ideocentric/caryatid/docs/indicators.md

# Indicators

Three indicators, and the reason there are three rather than one is a power
domain problem, not a design preference.

## The constraint

**Charging happens while the instrument is switched off.** The RGB LED hangs on
Seed GPIOs, and those are dark when the Seed is unpowered. So of the four states
worth showing, two cannot come from firmware at all:

| State | Needs the Seed powered? |
| --- | --- |
| Battery low while playing | yes — fine |
| Fault / warning | yes — fine |
| **Charging** | **no** |
| **Charge complete** | **no** |

Anything that must be readable with the instrument off has to be driven by
hardware. That is the whole argument.

## The three

**1. Switch lamp — power state.** The illuminated latching switch, fed from the
**5.0 V** boost rail. The switch asserts the boost's EN; the boost comes up; the
lamp lights. Off means genuinely off, with no firmware in the loop.

The lamp's **current limiting is internal**, so `R_LED` is a 0 Ω link. Keep the
0603 footprint so a different switch can be dropped in without a board change,
and because fitting a real resistor there is how this lamp gets dimmed if it is
ever wanted dimmer.

**Measured 2026-09-20**, and the part in hand is marked **3–6 V**, not the 3–9 V
variant this section was originally written against:

| Across the lamp | Current |
| --- | --- |
| 3.00 V | 5.6 mA |
| **5.00 V, the rail in service** | **28.5 mA** |
| 6.00 V, top of the marking | 39.9 mA *(extrapolated)* |

🔴 **The internal limiting is a plain series resistor, not a current source**:
three points fit Vf ~2.51 V with ~87.5 Ω to within 1%. A voltage-*range* marking
means the part tolerates the range, **not** that the current is constant over
it. Here it tracks the rail almost 8:1 end to end, which is why the budget
figure is quoted against a rail voltage.

**The brightness question is settled, and this section's own prediction was
right.** It said, conditionally, that a plain series resistor would give
"roughly 75% of the current" at 5 V against the 4×AA (~6 V) reference the
brightness was judged by. It is a plain series resistor and the real ratio is
28.5 / 39.9 = **71%**, which the eye reads as around 89% as bright. Almost
certainly indistinguishable, and comfortably inside a range the lamp already
sees on depleted NiMH. **No action, and no board change.**

**That reading is also the switch lamp's line in the 5 V budget**, where it was
the largest of three entries marked unknown and is now closed. It is the
**largest indicator load on the rail**, ahead of the RGB with all three dies
lit, and unlike the RGB it is lit whenever the instrument is on. See the
line-item table in [values.md](values.md) and
[`panel-latch-switch`](../discovery/findings/panel-latch-switch.yaml).

**2. Charge LED — charge state, hardware only.** Driven directly from the
bq24074's open-drain `/CHG` and `/PGOOD` off the OUT rail, via J4. **This is the
indicator that satisfies the charge-complete-while-off requirement**, and it is
the only one that must exist. Nothing about it depends on firmware running.

### One bicolour LED instead of two singles

J4 already carries a red/green **common-anode bicolour** with no board change. A
part like that has exactly three terminals and they land on pins 1–3 as they
stand; pin 4 stays unused, as it is now.

| J4 pin | Net | Bicolour |
| --- | --- | --- |
| 1 | `VOUT` | common anode |
| 2 | R9 1 kΩ → `~{CHG}` | red cathode |
| 3 | R10 1 kΩ → `~{PGOOD}` | green cathode |
| 4 | `GND` | unused |

It reads better than two separate LEDs, because the charger's two open-drain
outputs mix in one lens:

| `/CHG` | `/PGOOD` | Colour | Meaning |
| --- | --- | --- | --- |
| high-Z | high-Z | **off** | on battery, no charger |
| low | low | **amber** | charging |
| high-Z | low | **green** | external power, charge complete |
| low | high-Z | red | anomalous; should not occur |

Amber-while-charging going green-when-done is read without a legend, and it
matches the *off means fine* logic the RGB already uses.

> **The green die decides whether this works, and J4 runs from `VOUT`.** That is
> the cell, not a regulated rail — roughly **4.2 V falling to ~3.0 V** in use. An
> **AlGaInP** yellowish-green around 2.1 V is fine across the whole range. An
> **InGaN true green at 3.0–3.2 V will dim and then go dark as the cell drains**,
> and no resistor value fixes it. This is the same physics that stops the RGB
> being driven from 3V3, one rail down.

Current, with the dies now **measured** rather than assumed at ~2.1 V:

| Cell | Red | Green | Amber total |
| --- | --- | --- | --- |
| 4.2 V, full | 2.33 mA | 1.88 mA | 4.2 mA |
| 3.0 V, flat | 1.19 mA | 0.77 mA | 2.0 mA |

Each status pin sinks only its own, well inside the 15 mA limit. *(This section
read "2.1 mA per die" until 2026-09-22, derived from an assumed 2.1 V green. The
real green is 2.322 V, making it 1.88 mA. The 4.2 mA amber total survived the
correction by accident, since red's surplus covers green's shortfall.)*

**Expect to trim the balance**, and the direction is now measured: **red draws
24% more current than green** through equal resistors, on top of being the
brighter die per milliamp. R9 and R10 are separate resistors for exactly that.

🔴 **But the balance is not a fixed adjustment, it moves with state of charge.**
Green's higher forward voltage eats proportionally more of a shrinking headroom,
so green fades 2.4× across the cell's life while red fades 2.0×, and the amber
drifts toward red: a current ratio of 1.25 on a full cell against **1.55 on a
flat one**. Trim at mid-cell rather than on a freshly charged pack. Resistors can
centre this; they cannot stop it moving, because it is driven by the Vf
difference against a falling rail. Harmless, and arguably it reads correctly, but
it should not be rediscovered later and mistaken for a fault. See [`j4-charge-led`](../discovery/findings/j4-charge-led.yaml).

Part choice and its open question are in [sourcing.md](sourcing.md).

**3. RGB — everything else, firmware driven.** J12, on D26/D27/D29. Solid on/off
mixing only; no PWM.

> **It cannot be driven from a 3V3 GPIO.** Green and blue have forward voltages
> around 3.0-3.1 V against an output-high of roughly 3.15 V — they will not
> light, and no resistor value fixes it. **Common anode to the 5 V rail with the
> GPIOs sinking.** See [values.md](values.md).

**Tolerance confirmed against the datasheet**, not assumed. `DS12556` Rev 8,
Table 7, via the Daisy-to-STM32 mapping in `Seed_pinout.csv`:

| Daisy | STM32 | I/O structure | |
| --- | --- | --- | --- |
| D26 red | PD11 | **FT_h** | 5 V tolerant, high-speed low-voltage |
| D27 green | PG9 | **FT_h** | 5 V tolerant, high-speed low-voltage |
| D29 blue | PB14 | **FT_u** | 5 V tolerant, USB option on VDD33USB |

`FT` is 5 V tolerant, `TT` would be 3.3 V only. Positive injection is not
possible on an FT pin — there is no upper clamp to VDD, which is what the
tolerance consists of. Sink is 20 mA per I/O against the ~5 mA per channel here.

> **FIRMWARE: the internal pull-up and pull-down must stay disabled on D26, D27
> and D29.** `DS12556` Table 9 note 4: *"To sustain a voltage higher than 4 V the
> internal pull-up/pull-down resistors must be disabled."* These pins sit at the
> full 5 V whenever their LED is off, because the anode is on the 5 V rail. A
> GPIO configured with either pull enabled is outside the absolute maximum
> rating. Push-pull or open-drain output with no pull, and nothing else.

Files and links for both documents are in [datasheets.md](datasheets.md).

## RGB states

Seven colours from on/off mixing, urgency carried by blink rate, and **off means
fine** — which is what you want on a stage.

| Condition | Colour | Pattern | Source |
| --- | --- | --- | --- |
| Playing, battery OK | off | — | — |
| Battery low — head for a socket | amber | slow, 1 Hz | A10 |
| Battery critical | red | fast, 4 Hz | A10 |
| Fault | magenta | fast, 4 Hz | A10 + A11 |
| Charging | blue | solid | A11 |
| Charge complete | green | solid | A11 |

Cyan and white are deliberately unassigned. A spare state is worth more than an
exhaustive palette.

Firmware can show charge state on the RGB *while the instrument is on* because
it reads charge status from A11 — that is a convenience, not the mechanism that
satisfies the off-state requirement.

## Faults worth signalling

Magenta means something specific, or it means nothing:

- charger thermal fault or charge-timer expiry, via the `/CHG` behaviour on A11
- cell voltage critically low, via A10
- **cell disconnected or its protection tripped** — A10 reads near zero while
  the OUT rail is alive. Worth catching before a gig rather than during one.

## Charge status on one analogue pin

`/CHG` and `/PGOOD` are both open-drain, and the pin budget had no room for two
digital inputs. A11 had no other job, so both signals are encoded onto it as
four voltage levels: a pull-up to 3V3 and two different-valued pull-downs.

```
        3V3 ──[ 10k ]───┬──[ 1k ]──┬── A11
                        │          │
        /CHG ──[ 10k ]──┤        [10nF]
                        │          │
      /PGOOD ──[ 20k ]──┘         GND
              (2 x 10k series)
```

**Four resistors of one value** — the 0.1% 10 k already in stock (C374544).

| `/CHG` | `/PGOOD` | State | Level | Counts |
| --- | --- | --- | --- | --- |
| high-Z | high-Z | idle, on battery | 3.300 V | 4095 |
| high-Z | low | external power, not charging | 2.200 V | 2730 |
| low | high-Z | charging | 1.650 V | 2048 |
| low | low | charging, external present | 1.320 V | 1638 |

Minimum separation **330 mV** — 409 ADC counts — and because the parts are 0.1%
the worst case is **329 mV**, which is to say the nominal.

**Decode by nearest level, not by thresholds.** The bands cannot be confused, and
nearest-neighbour needs no constants that can later drift out of date.

### How the values were arrived at

A search over E24 maximising the minimum separation gives **10 k / 11 k / 18 k**
and 390 mV, against roughly 150 mV for the naive first pick. Monte-Carlo over
tolerance showed that network holding up well:

| Tolerance | Worst gap | Bands overlap |
| --- | --- | --- |
| 1% | 377 mV | no |
| 5% | 312 mV | **no** |

That it still works at 5% is what made the substitution safe. Separation here is
a threshold to clear, not a score to maximise: at 330 mV the closest two states
are 409 ADC counts apart, against noise of a few counts, so both networks are
unambiguous by a wide margin and the extra 60 mV is headroom nothing will ever
use. Meanwhile three values cost three BOM lines and three feeder positions
where one costs one — and the stocked part is 0.1%, so the one-value network's
worst case is 329 mV against its 330 mV nominal. Less accurate on paper, more
accurate in the drawer, cheaper to build. Reasoning in full in
[sourcing.md](sourcing.md).

Two things that are not obvious either way:

- **The levels depend only on the ratios**, so the network scales freely. 10 k is
  the largest value that keeps the ADC source impedance sane; scaling down only
  burns current for nothing.
- **The pull-up sits on 3V3, the Seed's rail**, so the network draws nothing
  while the instrument is off. The charger's status pins are alive then, but with
  no pull-up there is no path. Unlike the A10 battery divider, this costs no
  standby current at all.

`1k + 10nF` mirrors the A10 filter, and the capacitor is doing real work: at 10k
source impedance the ADC's sample-and-hold cannot charge fast enough on its own,
so the cap supplies it and the 10k merely tops the cap back up between samples.
**Use a long ADC sample time on A11 regardless.**

This also delivers requirement P-8 — charge state exposed to the MCU, not only
to LEDs — which had no implementation before.

## What is deliberately not here

**No PWM on the RGB.** Solid mixing only. Seven states is enough, and dimming a
status LED on a stage instrument is a feature nobody has asked for.

**No firmware involvement in the power lamp.** It follows the rail. A power
indicator that depends on software is a power indicator that lies during a hang.
