ideocentric/caryatid/docs/conventions.md

# Conventions for the tools

Rules that apply to **more than one tool**, and that each cost something to
learn. Every one of these lived in a single tool's docstring, where the next
tool to make the same mistake could not see it.

These are not style preferences. Each entry states the rule, the failure that
produced it, and the measurement that proves it — so a future change can tell
whether it is still true rather than taking it on faith.

For decisions about the *board*, see [decisions/](decisions/). This file is
about the code that edits it.

---

## 1. Recompute the zone fill before verifying a copper change

**Any tool that widens, moves, or adds copper must refill the zones before it
asks DRC whether the result is legal.**

A pour holds its clearance from a track by *retreating from it*. Change the
copper and check without refilling, and DRC compares new copper against a pour
drawn for the old geometry. The gap it measures is a fill artefact — a number
describing a board that will never be fabricated.

**What it cost.** `widen_necks.py` widened five Freerouting neck-downs to the
0.20 mm floor and DRC reported one new clearance violation:

```
zone clearance 0.3000 mm; actual 0.2630 mm
Track [/power/TMR] on F.Cu  vs  Zone 'GND plane' [GND]
```

0.263 is 0.300 minus half the 0.075 mm the track grew — the pour standing still.
Tested one at a time, **four of the five were already clean** and only TMR
"failed", against a fill that had not moved. The tool's all-or-nothing rule then
reverted all five. It had been printing "those necks are LOAD-BEARING … it needs
routing space, which is a placement question" since `a68ae67`. They were not,
and it did not.

**The tell:** the conflict was with a **zone**, which retreats, rather than with
a pad or another track, which cannot. A clearance violation against a pour, on
copper you just changed, is suspect until you have refilled.

```python
KPY = ".../Python.framework/Versions/3.9/bin/python3"
subprocess.run([KPY, "-c",
    f"import sys;sys.path.insert(0,'{KSP}');import wx;wx.App(False);"
    f"import pcbnew;b=pcbnew.LoadBoard('{path}');"
    f"pcbnew.ZONE_FILLER(b).Fill(b.Zones());pcbnew.SaveBoard('{path}',b)"])
```

`import wx; wx.App(False)` first — pcbnew's Python needs a wxApp to exist before
`ZONE_FILLER` runs, the same requirement `ImportSpecctraSES` has. It still
prints `create wxApp before calling this` on stderr and completes correctly;
that line is noise, not a failure.

**All-or-nothing verification is still right** — a half-widened board reads as
deliberate — but it multiplies the damage of a bad check. One false positive
reverted four sound repairs. Verify the board that would be fabricated.

---

## 2. Collect edits first, apply back to front, and check structure not just parens

Editing s-expression text while iterating over matches shifts every later
offset. Collect all `(offset, old, new)` first, then apply in **one** pass
sorted descending.

**"One pass" is load-bearing, and two descending passes are not equivalent.**
`silk_centre_roles.py` applied footprint-property edits and text edits in two
separate back-to-front passes, both measured against the same original string.
The first pass shifted the file under the second, and `ANALOG BUS` was spliced
inside another label's `(effects)` block.

**Parenthesis balance did not catch it**, because a splice moves parens without
changing their count. `lock_copper.py` corrupted the board the same way earlier,
dropping two segments while staying balanced. Balance is necessary and nowhere
near sufficient. Check structure as well:

```python
if t[off:off + len(old)] != old:
    sys.exit("offset no longer holds what was measured -- not writing")
top  = len(re.findall(r"^\t\(gr_text ", t, re.M))
if top != t.count("(gr_text "):
    sys.exit("a gr_text is no longer at top level -- not writing")
```

What actually surfaced the corruption was `kicad-cli` refusing to parse the
file. **A tool that writes a board should run `kicad-cli pcb drc` afterwards and
treat a non-zero exit as a failed write**, not only as a DRC result.

---

## 3. The collision box must share the anchor the emitter uses

A geometry model that tests one box and draws another is worse than no model:
it reports clearances confidently and wrongly.

- **`conn_labels.py`** tested a **centred** box and emitted `(justify bottom)`,
  which anchors the *bottom*. Every label drew about half a line higher than
  what was checked. The model called J3 a comfortable 0.73 mm clear of
  `CHG LEDS` while DRC reported them overlapping, **six times**, across 22 silk
  violations.
- **`silk_align_connectors.py`** built every reference box horizontally while
  preserving each field's *stored* angle. J9's reference was stored at 90° and
  drew vertical, so a 1.96 × 1.15 box was checked where the board drew
  1.15 × 1.96. The model read 0.47 mm of clearance; DRC found **0.2433**.
- **`pin_labels.surviving_labels`** used `x + up` on both sides of rotated text.
  `th_split` divides line height *asymmetrically* about the anchor, so every
  rotated label got a box of the wrong height, off centre.
- **`check_schematic.py`** made the same mistake in a different file format, and
  it is worth seeing twice. A net label in a `.kicad_sch` is anchored at the end
  that touches the wire and grows away from it; a symbol field is centred. A
  first version treated labels as centred, which halved their reach and reported
  a sheet clean while a 300 dpi plot showed labels plainly over the resistors.
  On `audio.kicad_sch`, `BIAS_E_L` anchors 8.89 mm from R51 and its text runs
  back toward it.

  🔴 **REFUTED 2026-08-24, and the correction belongs here rather than in a
  quiet edit.** Fixing the anchor was necessary and not sufficient: the box was
  still too SHORT, because `CHAR_W` was 0.72 mm per character and had never been
  measured despite a comment saying it was. Measured at 600 dpi off the plot
  this tool checks, it is 1.08–1.19 (`'+5V_RAW'` 8.297 mm / 7, `'VOUT'`
  4.612 mm / 4, `'LEG_101_L'` 9.700 mm / 9). A 1.6× underestimate on every box.

  Everything that rested on it was wrong. `BIAS_E_L` does not clear R51 by
  0.59 mm, it runs **3.01 mm into it**. Thirty labels cross, not zero. And the
  five "cosmetic" crossings fixed by moving them 2.54 mm were sized from the
  same broken model, which called a 3 mm overshoot 0.13 mm — **the fix was
  scaled by the error it was correcting, so it could not have worked.**

  The rendered plot had shown this correctly at 100 dpi and again at 300, and was
  overruled both times by the model, because a number feels like evidence and a
  picture feels like an impression. Neither is evidence about the other: the
  plot IS the artefact being checked, and the model is only a claim about it.

  The general form of this (why the constant survived so long, and what a
  constant has to carry so it cannot) is **rule 10**. This entry is the local
  damage; rule 10 is the rule.

- **`check_schematic.py`'s border test, again, and this one was found by eye.**
  It compared the symbol **origin** against the frame and skipped every symbol
  whose reference starts with `#`. Both are the same error as above in a
  different disguise: a box smaller than the ink. C21 on `panel-io.kicad_sch`
  had its origin at y 407.67, inside the 410 frame, while its lower pin reached
  **411.48** — `Device:C` has a body half-height of 0.762 mm and pins reaching
  3.81 mm, a factor of five. Underneath it the `GND` flag sat at 416.56 with its
  bottom edge **0.9 mm from the paper edge**, and was never tested at all,
  because the `#PWR` filter written for the *label-crossing* check had been
  copied into the *border* check where it does not belong. A power flag is ink
  on the plot like anything else.

  The fix keeps `lib_extents()` body-only and adds a separate `lib_reach()`
  including pins, because the two checks ask different questions. "Does this
  label sit on the part" tolerates a label along a pin stub; "is any ink off
  the page" does not.

Where the anchor cannot be established, **over-reserve**. An obstacle model may
claim more space than the ink needs; it may never claim less.

**A filter is part of a check, not part of the file.** Three of the five misses
above are a box or an exclusion carried from the place it was correct into a
place it was not. When copying a guard between checks, restate what it is for;
if that sentence does not survive the move, neither should the guard.

---

## 4. `P.tw` is a bounding box, so centre with it and never right-align with it

`pin_labels.tw()` returns KiCad's bounding-box width — about 1.1× the inked
width plus a constant. That error is not uniform: it **grows with string
length**.

- **Centring is safe.** The surplus splits evenly either side of a centred
  anchor and cancels; the drawn centre is the anchor whatever the error.
- **Computing an edge is not.** Placing labels at `right - w/2` to right-align
  them indented `GND` about 0.11 mm further than `R`, because the 3-character
  string carries more surplus. The right edges were identical in the model and
  visibly ragged on the board.

To align an edge, emit `(justify right)` and let KiCad find the true edge. The
box then extends *leftward* from the anchor, where over-estimating is the safe
direction.

---

## 5. Silk geometry is centrelines; footprint bounding boxes include markers

Two distinct traps in reading a footprint's silkscreen.

**`fp_line` coordinates are the middle of a 0.12 mm stroke.** The drawn edge is
0.06 mm further out. `silk_audio_baseline.py` measured 0.280 mm of clearance
where DRC found **0.2158**, on J14 and J18. J17's outline ends 0.14 mm sooner
and passed — the kind of near-miss that makes a wrong model look right.

**The bounding box of *all* silk is not the body.** J5 and J11 are IDC box
headers carrying a pin-1 triangle *outside* the outline — J5's at
x 161.780‥162.780 against a body ending at 161.390. Centring on the union put
the label 0.695 mm off, while the body outline, the pad span and the courtyard
all independently agreed on 156.830. Group the segments into connected
components and take the largest; a detached marker then drops out by
construction, with no per-part exception list.

---

## 6. Normalise a lone outlier; exclude only what cannot be fixed

An allow-list is for defects that **cannot** be repaired. Reaching for one to
silence something cheap to fix hides a real inconsistency behind a written
excuse.

**R45** was flagged `lib_footprint_mismatch` because its pads were stored at
270° against a footprint at 90° — 180° *relative*, where `Resistor_SMD` has 0°.
It was **the only one of 64 0603 resistors** on this board like that. The half
turn was harmless (a 0.800 × 0.950 mm rectangle is unchanged by it, and both pad
centres are byte-identical before and after), which is exactly why excusing it
was wrong. It was normalised; the allow-list entry became a comment saying so.

**A1 and A2** are the opposite and belong in the list. All 20 pads of each were
diffed against `caryatid.pretty/DaisySeed_Socket_A_1x20.kicad_mod`: **none
differ**. What differs is what KiCad adds when a footprint is *placed* — `path`,
`sheetfile`, `sheetname`, two property fields and their hide flags. None of it
is copper, and none of it is removable without breaking the schematic link.

The test is not "is it harmless" — both were harmless. It is **"can it be
fixed"**.

---

## 7. Record a hand placement as an override rather than overwriting it

A generator that re-derives positions will revert a deliberate hand adjustment
on its next run, silently, and the person who made it will not be watching.

`silk_audio_baseline.py` carries `ROLE_OVERRIDE` and `REF_OVERRIDE` for J14,
whose `MIC RTN` and reference were placed by hand after the computed positions
read wrong on the shortest jack. Re-running the tool now reproduces the board
instead of fighting it.

Locks are not sufficient: a tool that strips and regenerates its own output by
uuid ignores them. Locks stop an accident; recording the intent stops a re-run.

---

## 8. A fact carried only in conversation will outlive its truth

Not a coding rule, but it cost the most sessions.

An "R45 sits 1.22 mm from the board edge, review with the enclosure in hand"
concern was repeated across four sessions and was never true after `3fe330e`
moved the part. Measured: **5.500 mm**, with J15 and J9 both reaching *further*
toward that edge than R45 does. It survived because it was never written into a
ledger record where it would have been re-checked — the precise failure
`~/.claude/CLAUDE.md`'s ledger methodology exists to prevent. It is now retired
as dated evidence on `BUD-CU-477-interior`.

If a claim matters enough to repeat, it belongs in
[discovery/findings/](../discovery/findings/), not in a summary.

---

## 9. A `.kicad_sch` is not a `.kicad_pcb`, in two ways that will bite

Both of these cost real time in `check_schematic.py`, and neither is guessable
from experience with the board format.

**A schematic embeds its symbol LIBRARY beside its placed instances, and the two
are indistinguishable by their opening line.** Both are `(symbol ...)` at the
same nesting. Matching both reported **49 symbols outside the page borders**,
with references like `J`, `C` and `R` carrying no number and coordinates near
the origin, because those were library definitions in symbol-local coordinates.

```python
if "(lib_id " not in blk:      # a placed instance has one; a definition does not
    continue
```

The real answer was **one** symbol, JP6 in a title block. A checker that
overcounts by fifty is worse than no checker: the finding that mattered was
buried in noise that looked identical to it.

**Property coordinates are ABSOLUTE in a schematic and RELATIVE in a board.** In
a `.kicad_pcb`, a footprint's Reference sits at an offset from the footprint
origin and has to be transformed by the footprint's rotation. In a
`.kicad_sch`, the same field carries a page coordinate directly. Verified rather
than assumed: R11's symbol sits at (190.5, 69.85) and its reference text at
(196.5, 39.85).

Carrying the board habit across produces offsets that look plausible and are
nonsense, which is the failure mode that does not announce itself.

**The corollary for symbol extents.** A placed instance does not record how big
its body is; that lives in the embedded library definition, in symbol-local
coordinates. Any check that needs a body size has to read `lib_symbols` and
match on `lib_id`, or guess. A guess that fits a resistor is wrong for a
twenty-pin connector, and a check calibrated on passives will silently miss
every collision on the parts that matter.

---

## 10. An empirical constant carries its measurement, or it is a guess wearing a lab coat

**Any constant standing in for a physical measurement must record the raw
observation that produced it: what was measured, the sample, and the number
before rounding.** A constant that merely *claims* provenance cannot be audited,
and everything computed from it inherits the error silently.

```python
CHAR_W = 0.72          # width per character at 1.27 mm text, measured off a plot
```

It was not measured off a plot. It was a guess, and the comment is what made it
survive: the line reads as settled, so nobody re-derives it, and there is nothing
in it to check against. Measured at 600 dpi off the very plots the tool checks:

| string | chars | inked width | mm/char |
| --- | --- | --- | --- |
| `+5V_RAW` | 7 | 8.297 mm | 1.185 |
| `VOUT` | 4 | 4.612 mm | 1.153 |
| `LEG_101_L` | 9 | 9.700 mm | 1.078 |

**A 1.6× underestimate on every text box in the file**, for weeks.

**What it cost.** Not one wrong number, but a wrong number that every later
measurement was expressed in:

- `BIAS_E_L` does not clear R51 by 0.59 mm. It runs **3.01 mm into it**. That
  0.59 was quoted across four sessions, written into rule 3 above as established
  fact, and used to overrule a 100 dpi plot and then a 300 dpi one.
- **Thirty labels crossed while the checker reported zero.**
- Five of them were "fixed" by moving them 2.54 mm, a distance taken from the
  same model, which called a 3 mm overshoot 0.13 mm. **The repair was sized by
  the error it was repairing**, so it could not have worked, and it was committed
  and reported as done.

**The tell is a model that keeps winning arguments against the artefact.** The
plot showed those crossings correctly, twice, and lost to the geometry both
times, because a number reads as evidence and a picture reads as an impression.
Neither is evidence *about the other*: the plot is the thing being checked and
the model is only a claim about it. **When a model and a rendering disagree,
measure the rendering.** That is the tie-break, and it is cheap: `pdftoppm -r
600` and a pixel span settled in minutes what four sessions of arguing had not.

The same trap in a smaller size: `NEAR = 0.6` and `DEEP = 0.60` are thresholds
about how a plot *reads*, not measurements, and they say so. A constant that
cannot cite an observation should admit it is a judgement, so the next person
knows which kind of thing they are looking at.

**Scope.** This is not a demand to measure integers and grid pitches, which come
from the file and are exact. It applies to any constant standing in for something
physical or rendered: text metrics, stroke widths, clearances read off a plot,
anything whose truth lives outside the source and can drift from it.
