ideocentric/caryatid/discovery/evidence/2026-09-23-board-1-top.jpg

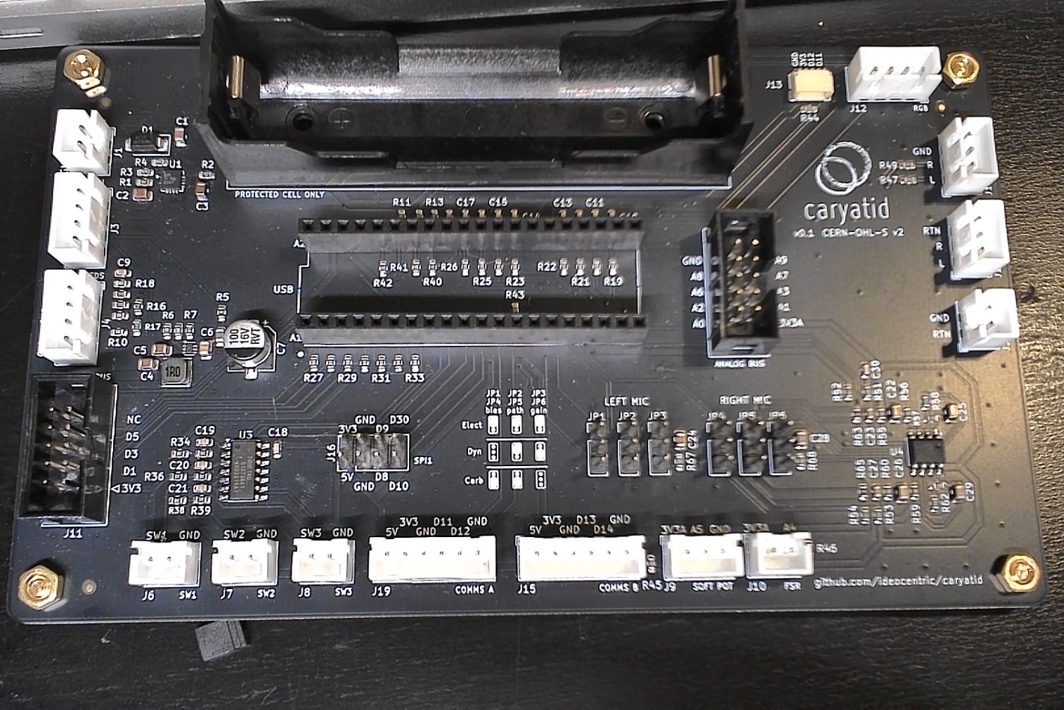
discovery/evidence/2026-09-23-board-1-top.jpg
