ideocentric/caryatid/discovery/evidence/2026-09-23-board-3-bottom.jpg

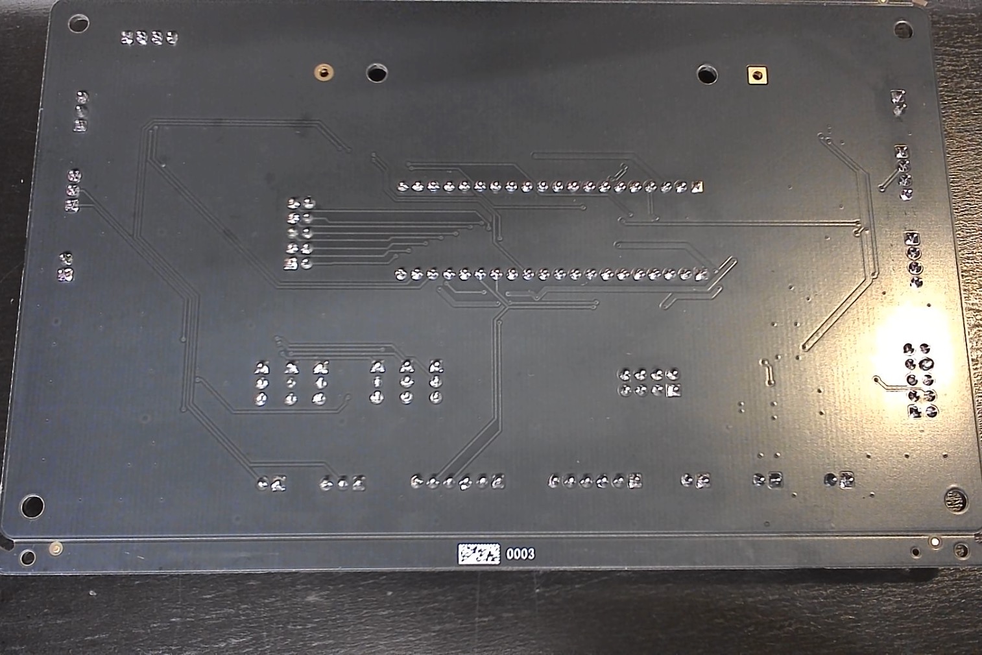
discovery/evidence/2026-09-23-board-3-bottom.jpg
