ideocentric/caryatid/discovery/evidence/2026-09-23-board-5-top.jpg

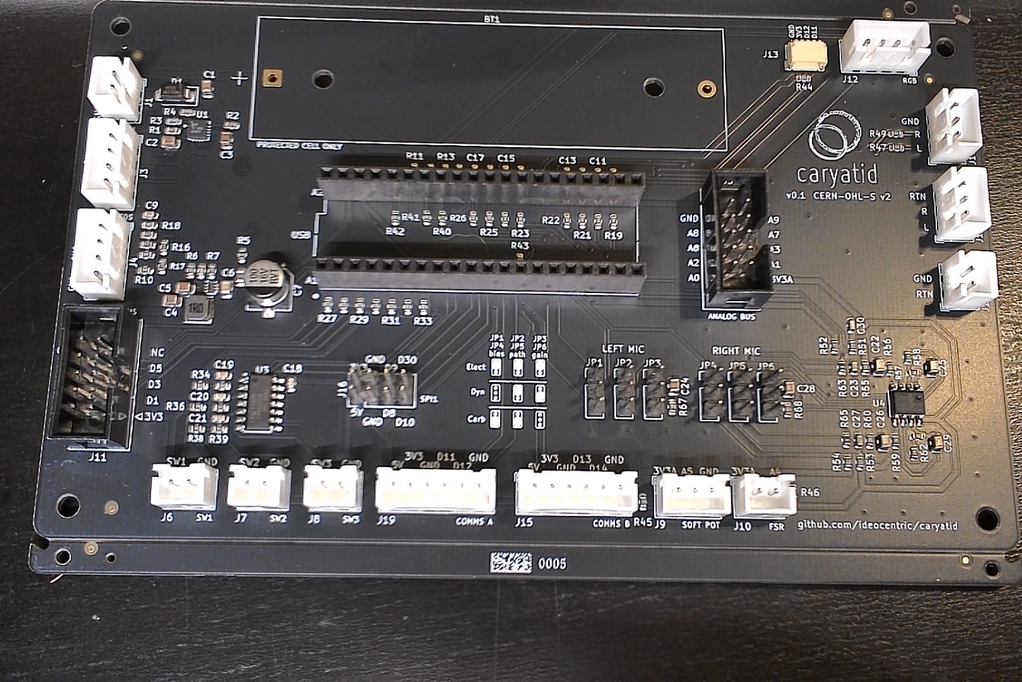
discovery/evidence/2026-09-23-board-5-top.jpg
