ideocentric/caryatid/discovery/evidence/2026-08-21-audio-netlist-diff.txt

2026-08-21 — audio + panel-io netlist diff, ADR 0010

before: HEAD ad6a54d, 16 dnp symbols across audio (12) and panel-io (4)
after:  right channel jumpered (JP4/JP5/JP6 + R68), R48/R50/R64/R66 deleted,
        R43-R46 assembled. 0 dnp symbols on any sheet.

kicad-cli 9.0.6 sch export netlist --format kicadsexpr, both states.
ERC: 0 violations at --severity-all after every step.

nets before 107  after 113
NEW NET     /audio/BIAS_C_R ['JP4.3', 'R54.2']
NEW NET     /audio/BIAS_E_R ['JP4.1', 'R53.2']
NEW NET     /audio/LEG_101_R ['JP6.1', 'R62.2']
NEW NET     /audio/LEG_256_R ['JP6.3', 'R68.2']
NEW NET     AMP_OUT_R ['C29.2', 'JP5.1']
NEW NET     BYPASS_R ['JP5.3', 'R65.2']
CHANGED     /audio/GAINLEG_R
       - ['R62.2']
       + ['JP6.2']
CHANGED     /audio/MIC_R
       - ['R53.2', 'R54.2']
       + ['JP4.2']
CHANGED     /audio/OPA_R_N
       - []
       + ['R68.1']
CHANGED     /audio/OUT_L_J
       - ['R48.1']
       + []
CHANGED     /audio/OUT_R_J
       - ['R50.1']
       + []
CHANGED     AUDIO_IN_R
       - ['C29.2', 'R65.2', 'R66.1']
       + ['JP5.2']
CHANGED     BYPASS_L
       - ['R64.1']
       + []
CHANGED     GND
       - ['R48.2', 'R50.2', 'R64.2', 'R66.2']
       + []
byte-identical nets: 99
